joebritt/usb2cmi_lightpen/interface_photos/V2/IMG_20200309_125538.jpg

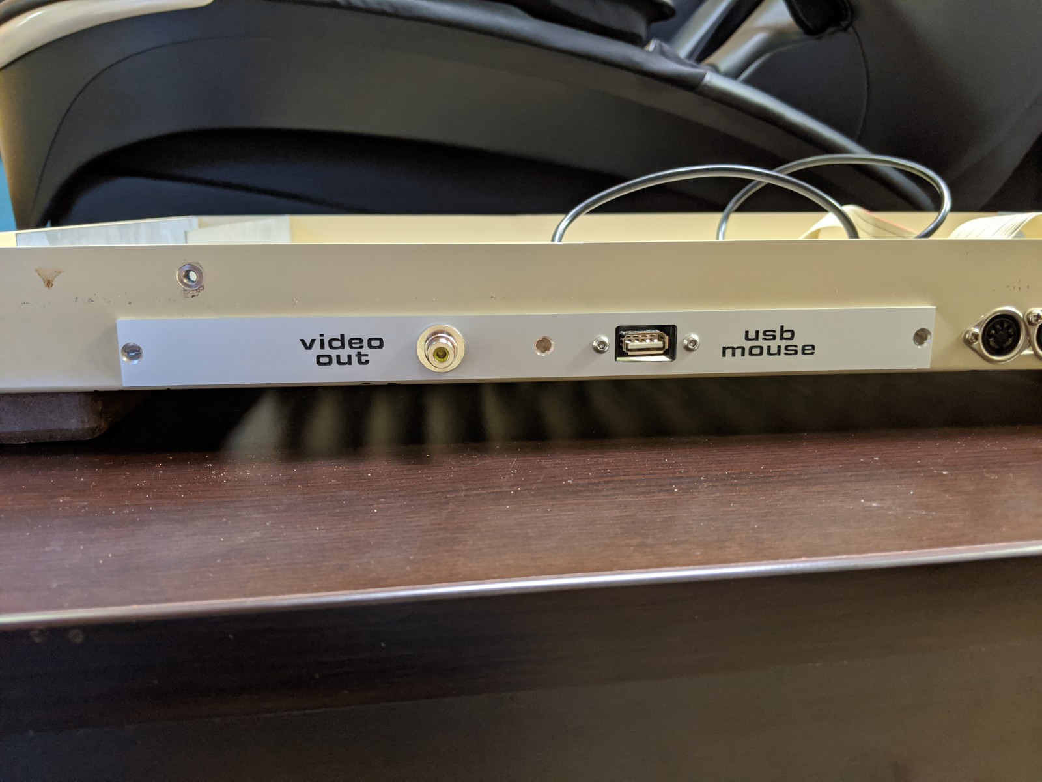
interface_photos/V2/IMG_20200309_125538.jpg
