joebritt/usb2cmi_lightpen/interface_photos/V2/IMG_20200321_205620.jpg

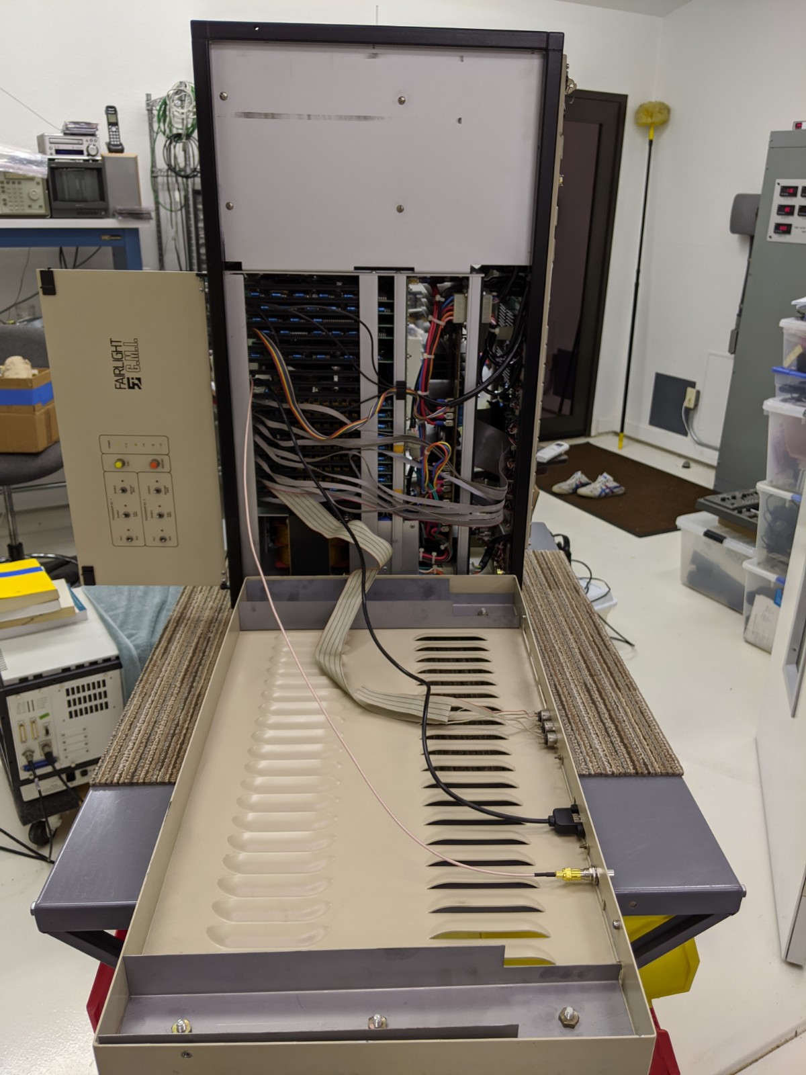
interface_photos/V2/IMG_20200321_205620.jpg
