joebritt/usb2cmi_lightpen/interface_photos/V2/IMG_20200321_212625.jpg

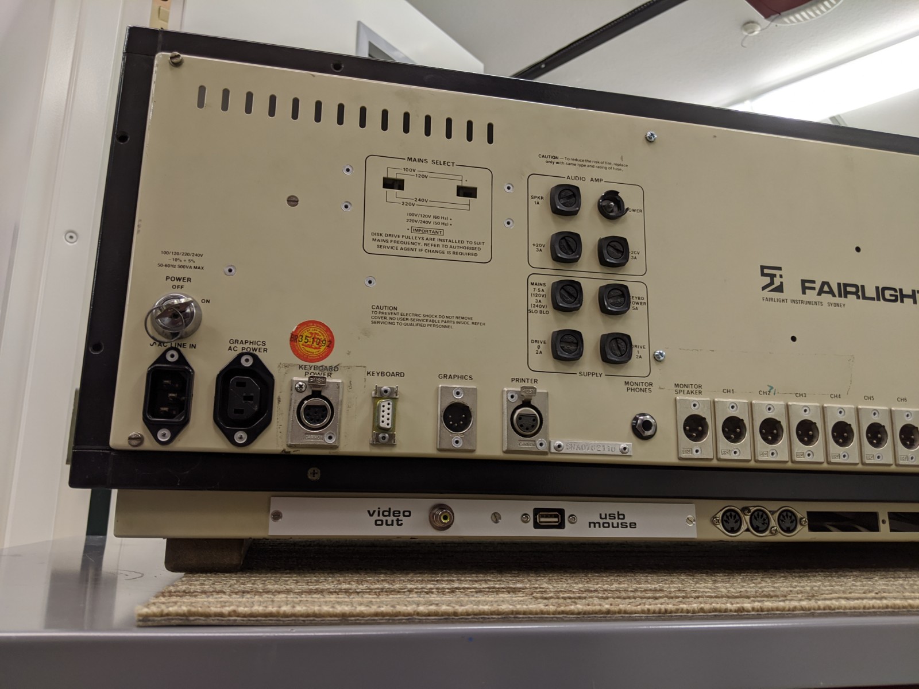
interface_photos/V2/IMG_20200321_212625.jpg
