joebritt/usb2cmi_lightpen/interface_photos/V2/IMG_20200322_163101.jpg

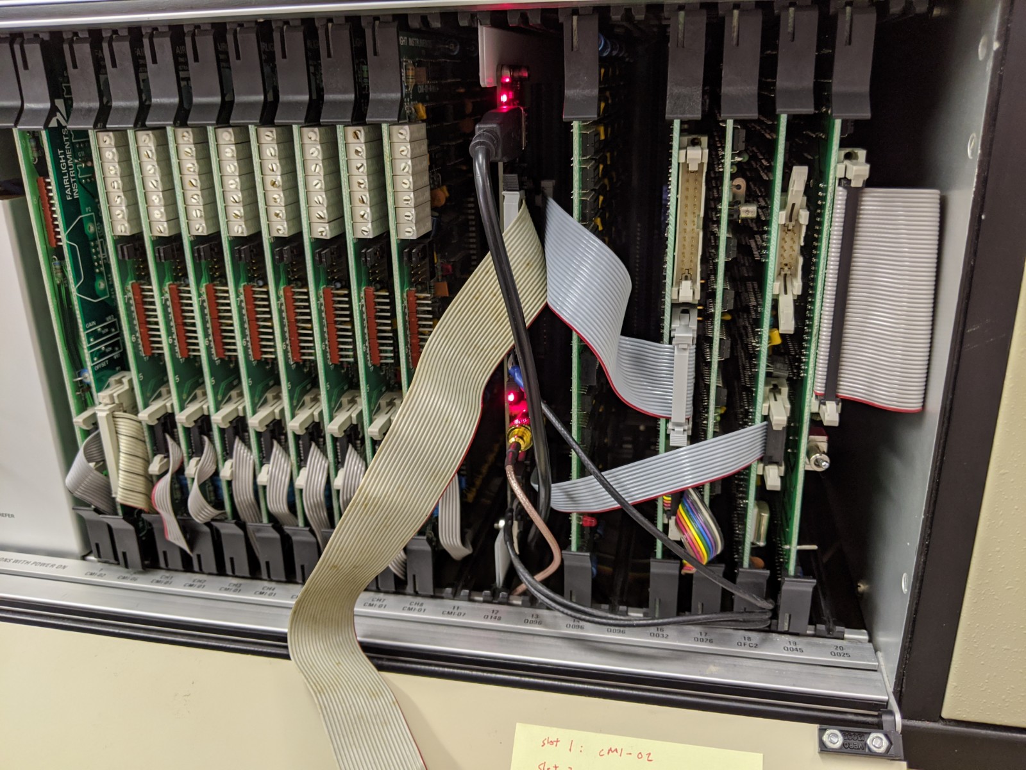
interface_photos/V2/IMG_20200322_163101.jpg
