joebritt/usb2cmi_lightpen/interface_photos/V2/IMG_20200322_164144.jpg

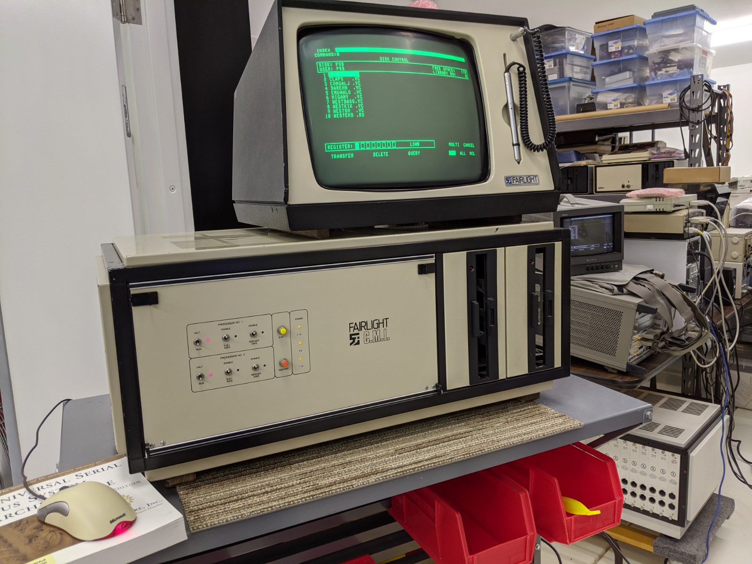
interface_photos/V2/IMG_20200322_164144.jpg
