joebritt/usb2cmi_lightpen/mouse/2x_only_pos.h

// This table was generated with an excel spreadsheet.
//
// The clock used to drive the Output Compare pulse generator runs at
// 80MHz.  The CMI dotclock is 10.38MHz.
//
// The screen is broken into 5 horizontal zones, and the number of
// 80MHz clocks we count to get into the pixel position we want
// varies depending on which zone the cursor is in.

int pixel_offsets[512] = { 
1017, 
1025, 
1033, 
1041, 
1048, 
1056, 
1064, 
1071, 
1079, 
1087, 
1095, 
1102, 
1110, 
1118, 
1125, 
1133, 
1141, 
1149, 
1156, 
1164, 
1172, 
1179, 
1187, 
1195, 
1202, 
1210, 
1218, 
1226, 
1233, 
1241, 
1249, 
1256, 
1264, 
1272, 
1280, 
1287, 
1295, 
1303, 
1310, 
1318, 
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
};
