joebritt/usb2cmi_lightpen/mouse/pos_II.h

// This table was generated with an excel spreadsheet.
//
// The clock used to drive the Output Compare pulse generator runs at
// 80MHz.  The Series I/II CMI dotclock is 10.65MHz.
//
// Note that the Q045 graphics card has 2 pots (RV1 and RV2) that 
// control one-shots which determine the active area location
// and width.
// Because of that, it is not safe for us to assume hard values
// for the bias offset and right edge of the screen.
// For Q045 systems, we allow the cursor to run off the screen on either side.
// We can safely pin the top and bottom positions, however.

unsigned int pixel_offsets_II[512] = { 
900,
908,
916,
923,
931,
938,
946,
953,
961,
968,
976,
983,
991,
998,
1006,
1013,
1021,
1028,
1036,
1043,
1051,
1058,
1066,
1073,
1081,
1088,
1096,
1103,
1111,
1118,
1126,
1133,
1141,
1148,
1156,
1163,
1171,
1178,
1186,
1193,
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
};
