joebritt/usb2cmi_lightpen/bootloader/boot_config.h

/*
*******************************************************************************
                                                                                
Software License Agreement                                                      
                                                                                
Copyright © 2007-2008 Microchip Technology Inc. and its licensors.  All         
rights reserved.                                                                
                                                                                
Microchip licenses to you the right to: (1) install Software on a single        
computer and use the Software with Microchip 16-bit microcontrollers and        
16-bit digital signal controllers ("Microchip Product"); and (2) at your        
own discretion and risk, use, modify, copy and distribute the device            
driver files of the Software that are provided to you in Source Code;           
provided that such Device Drivers are only used with Microchip Products         
and that no open source or free software is incorporated into the Device        
Drivers without Microchip's prior written consent in each instance.             
                                                                                
You should refer to the license agreement accompanying this Software for        
additional information regarding your rights and obligations.                   
                                                                                
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
*******************************************************************************

The boot loader uses three interfaces to define and customize its behavior.

Boot Loader IO Interface:

The boot loader IO interface definitions provide control inputs and status
outputs that the boot loader can use to determine when it should load a new
application image and how it should report its status.

Boot Loader Media Interface:

The boot loader media interface definitions provide access to the boot image 
medium and the ability to read the file.

Boot Loader Interface

The Loader interface definitions provide any data translation and Flash 
programming necessary to load the boot image into program Flash memory.

These interface routines can be implemented via macros or functions as 
required.
*******************************************************************************

 Change History:
  Rev   Description
  ----  -----------------------------------------
  2.7   Updated to include the PIC32 device information.

        Updated to include additional error codes (BL_FILE_NO_DATA, 
        LOADER_MISSING_START, LOADER_ALIGNMENT, LOADER_ERR, and
        LOADER_EOF_REC_MISSING)

*******************************************************************************
*/

/* Boot Status Codes
**************************************************************************
BOOT_STATUS is used to identify the current status of the boot loader.
**************************************************************************
*/

typedef enum
{
    // Boot loader status
    BL_RESET = 0,           // Device has been reset
    BL_LOADING,             // Loading of a new application image activated
    BL_TRANSPORT_INIT,      // Boot loader transport layer initialized
    BL_MEDIUM_DETACH,       // Indicates that the boot medium has been detached
    BL_FOUND_FILE,          // New application image file has been found
    BL_PROGRAMMED,          // The application image has been programmed to Flash
    BL_BOOTING,             // Booting application image

    // Transport-specific errors
    BL_USB_OC_ERR,          // USB Over-current error detected
    BL_FS_INIT_ERR,         // Unable to initialize the boot medium's file system
    BL_USB_HUB_ERR,         // USB hub error (hubs not supported)
    BL_BAD_DEV_ERR,         // Unsupported USB device attached
    USB_ENUM_ERR,           // Unable to enumerate USB device
    USB_MSD_INIT_ERR,       // Unable to initialize USB MSD client driver
    OUT_OF_MEMORY_ERR,      // Attempted to malloc memory and failed
    BL_FILE_ERR,            // Unable to open the boot image file
    BL_FILE_NO_DATA,        // Unable to read data from file but file did not report EOF
    USB_ERR,                // Unspecified USB error

    // Loader Errors
    LOADER_ADDRESS_LOW,     // Flash block address is out of range, low
    LOADER_ADDRESS_HIGH,    // Flash block address is out of range, high
    LOADER_CHECKSUM_ERR,    // Hex record checksum didn't match
    LOADER_FLASH_ERASE_ERR, // Erase had an error
    LOADER_FLASH_WRITE_ERR, // Unable to write to Flash
    LOADER_FLASH_VERIFY_ERR,// Data written to Flash did not match buffer data
    LOADER_MISSING_START,   // Start code was missing from the start of a line
    LOADER_ALIGNMENT,       // There was an issue with the data alignment
    LOADER_ERR,             // Unspecified error in the loader
    LOADER_EOF_REC_MISSING, // Reached the end of the file stream without a hex EOF record

    // General errors
    BL_BOOT_FAIL,           // Application not valid or failed to launch
    BL_FILE_NOT_FOUND       // Application image file not found

} BOOT_STATUS; 


/*
*******************************************************************************
Boot Loader IO Configuration
*******************************************************************************
*/

/* Boot Loader IO Call Out Interfaces
*******************************************************************************
The following interfaces are defined by macros and called from the boot loader 
to customize and define its control and status IO behavior.
*******************************************************************************
*/

#define BLIO_LoaderEnabled()    TRUE

extern volatile BOOT_STATUS BootStatus;
//#define BLIO_ReportBootStatus(s,z)            (BootStatus=(s))
//#define BLIO_ReportBootStatus(s,z)            Serial_BootStatus(s,z)
void BLIO_ReportBootStatus ( BOOT_STATUS status, char *message );

//*****************************************************************************
// Boot Loader Media Interface Configuration
//*****************************************************************************

// Application Image File Name
#define BOOT_FILE_NAME          "cmimouse.hex"

// Defines the size of the buffer used to read the boot image file.
#define BL_READ_BUFFER_SIZE     512


/* Boot Loader Media Interface Call Outs
*******************************************************************************
The following interface routines are called from the boot loader to access new
application image file and program it to Flash.
*******************************************************************************
*/

#define BLMedia_InitializeTransport()       USBInitialize(0)

#if defined(__PIC32__)
#define BLMedia_DeinitializeTransport()     (USBHostShutdown(),IFS1CLR = 0x02000000)
#else
#define BLMedia_DeinitializeTransport()     (USBHostShutdown())
#endif

#define BLMedia_MediumAttached()            USBHostMSDSCSIMediaDetect()


/* "Loader" Interface Call Outs
*******************************************************************************
The following interface is used by the media layer to decode and program the 
image file to memory.
*******************************************************************************
*/

// These macros define the maximum size of a Flash block.

#if defined(__32MX460F512L__) || \
    defined(__32MX440F512H__) || \
    defined(__32MX775F512L__) || \
    defined(__32MX675F512L__) || \
    defined(__32MX695F512L__) || \
    defined(__32MX795F512L__) || \
    defined(__32MX575F512L__) || \
    defined(__32MX795F512H__) || \
    defined(__32MX775F512H__) || \
    defined(__32MX695F512H__) || \
    defined(__32MX675F512H__) || \
    defined(__32MX575F512H__)

    #define FLASH_BLOCK_SIZE            (1024 * 4)          // Size in bytes

    //This set of options will only work with optimazation setting -Os
    //  Address of main application's Startup code
    #define APPLICATION_ADDRESS         0x9D00E000
    //  Base address and length of user flash block
    #define PROGRAM_FLASH_BASE          0x1D00E000          // Physical address
    #define PROGRAM_FLASH_LENGTH        0x00072000          // Length in bytes

//    //This set of options will only work with optimazation settings -Os, -O1, and -O2
//    //  Address of main application's Startup code
//    #define APPLICATION_ADDRESS         0x9D010000
//    //  Base address and length of user flash block
//    #define PROGRAM_FLASH_BASE          0x1D010000          // Physical address
//    #define PROGRAM_FLASH_LENGTH        0x00070000          // Length in bytes
//
//    //This set of options will work with all optimazation settings
//    //  Address of main application's Startup code
//    #define APPLICATION_ADDRESS         0x9D017000
//    //  Base address and length of user flash block
//    #define PROGRAM_FLASH_BASE          0x1D017000          // Physical address
//    #define PROGRAM_FLASH_LENGTH        0x00069000          // Length in bytes

#elif defined(__32MX460F256L__) || \
      defined(__32MX440F256H__) || \
      defined(__32MX775F256L__) || \
      defined(__32MX675F256L__) || \
      defined(__32MX575F256L__) || \
      defined(__32MX775F256H__) || \
      defined(__32MX675F256H__) || \
      defined(__32MX575F256H__)

    #define FLASH_BLOCK_SIZE            (1024 * 4)          // Size in bytes

    //This set of options will only work with optimazation setting -Os
    //  Address of main application's Startup code
    #define APPLICATION_ADDRESS         0x9D00E000
    //  Base address and length of user flash block
    #define PROGRAM_FLASH_BASE          0x1D00E000          // Physical address
    #define PROGRAM_FLASH_LENGTH        0x00032000          // Length in bytes

//    //This set of options will work with all optimazation settings
//    //  Address of main application's Startup code
//    #define APPLICATION_ADDRESS         0x9D017000
//    //  Base address and length of user flash block
//    #define PROGRAM_FLASH_BASE          0x1D017000          // Physical address
//    #define PROGRAM_FLASH_LENGTH        0x00029000          // Length in bytes
//
//    //This set of options will only work with optimazation settings -Os, -O1, and -O2
//    //  Address of main application's Startup code
//    #define APPLICATION_ADDRESS         0x9D010000
//    //  Base address and length of user flash block
//    #define PROGRAM_FLASH_BASE          0x1D010000          // Physical address
//    #define PROGRAM_FLASH_LENGTH        0x00030000          // Length in bytes

#elif defined(__32MX440F128H__) || \
      defined(__32MX440F128L__)

    #define FLASH_BLOCK_SIZE            (1024 * 4)          // Size in bytes

// Joe Britt -- this seems to work with optimizations setting -01
    //  Address of main application's Startup code
    #define APPLICATION_ADDRESS         0x9D00D000
    //  Base address and length of user flash block
    #define PROGRAM_FLASH_BASE          0x1D00D000          // Physical address
    #define PROGRAM_FLASH_LENGTH        0x00013000          // Length in bytes

// Joe Britt -- this was the setting I was using, then I realized it looks like I can squeeze
//              things for some more space
//    //This set of options will only work with optimazation setting -Os
//    //  Address of main application's Startup code
//    #define APPLICATION_ADDRESS         0x9D00E000
//    //  Base address and length of user flash block
//    #define PROGRAM_FLASH_BASE          0x1D00E000          // Physical address
//    #define PROGRAM_FLASH_LENGTH        0x00012000          // Length in bytes

//    //This set of options will only work with optimazation settings -Os, -O1, and -O2
//    //  Address of main application's Startup code
//    #define APPLICATION_ADDRESS         0x9D010000
//    //  Base address and length of user flash block
//    #define PROGRAM_FLASH_BASE          0x1D010000          // Physical address
//    #define PROGRAM_FLASH_LENGTH        0x00010000          // Length in bytes
//    
//    //This set of options will work with all optimazation settings
//    //  Address of main application's Startup code
//    #define APPLICATION_ADDRESS         0x9D017000
//    //  Base address and length of user flash block
//    #define PROGRAM_FLASH_BASE          0x1D017000          // Physical address
//    #define PROGRAM_FLASH_LENGTH        0x00009000          // Length in bytes


#elif defined(__PIC24F__)

#define APPLICATION_ADDRESS         0xA000

// These macros define the maximum size of a Flash block.
#define PROGRAM_FLASH_BASE          0x0000A000          // Physical address
//#define PROGRAM_FLASH_LENGTH        0x00020C00          // Length in bytes - this includes the configuration words
#define PROGRAM_FLASH_LENGTH        0x00020800          // Length in bytes - this does not include the configuration words

#define FLASH_BLOCK_SIZE            (1024)          // Size in bytes

#else
    #error "Device currently supported"
#endif

// Optional Record Type Support (Necessary if EXTENDED_HEXFILE_SUPPORT is defined)
#define Loader_ValidateSerialNumber(d,l)    RECORD_NON_DATA
#define Loader_ValidateRevisionNumber(d,l)  RECORD_NON_DATA
#define Loader_CheckErrorDetection(d,l)     RECORD_NON_DATA

#define Loader_PermitProgramming()          TRUE


/*
*******************************************************************************
EOF
*******************************************************************************
*/
