joebritt/usb2cmi_lightpen/bootloader/boot_io.c

/*
********************************************************************************
                                                                                
Software License Agreement                                                      
                                                                                
Copyright © 2008 Microchip Technology Inc. and its licensors.  All         
rights reserved.                                                                
                                                                                
Microchip licenses to you the right to: (1) install Software on a single        
computer and use the Software with Microchip 16-bit microcontrollers and        
16-bit digital signal controllers ("Microchip Product"); and (2) at your        
own discretion and risk, use, modify, copy and distribute the device            
driver files of the Software that are provided to you in Source Code;           
provided that such Device Drivers are only used with Microchip Products         
and that no open source or free software is incorporated into the Device        
Drivers without Microchip's prior written consent in each instance.             
                                                                                
You should refer to the license agreement accompanying this Software for        
additional information regarding your rights and obligations.                   
                                                                                
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
********************************************************************************
*/

#include "Compiler.h"
#include "GenericTypedefs.h"
#include "HardwareProfile.h"
#include "boot.h"

/*
*******************************************************************************
Boot Loader IO Configuration
*******************************************************************************
*/

// Calculates the CORE_TICK_PERIOD for the status LED blink period.
#ifndef FOSC
    #define FOSC                    72E6
#endif

#ifndef TOGGLES_PER_SEC
    #define TOGGLES_PER_SEC			10
#endif

#ifndef CORE_TICK_PERIOD
    #define CORE_TICK_PERIOD	    (FOSC/2/TOGGLES_PER_SEC)
#endif

// Selects the status LED (port B only) used to indicate boot status.
#ifndef BOOT_LED
    #define BOOT_LED                BIT_7
#endif


// Global Data
volatile unsigned int   TickPeriod;     // LED Flash timer tick

volatile BOOT_STATUS    BootStatus;     // Most recent boot status reported

BOOL                    SwitchPrimed;   // Boot switched released so it can
                                        // be used as an abort if needed


/****************************************************************************
  Function:
    void BLIO_InitializeIO ( void )

  Description:
    This routine initializes the status LED and boot switch ports.  It also 
    initializes the core timer so it can be used to flash the status LED.

  Precondition:
    None

  Parameters:
    None

  Returns:
    None

  Remarks:
    None
***************************************************************************/

void BLIO_InitializeIO ( void )
{
	hw_init();		// set up our board-specific i/o
}


/****************************************************************************
  Function:
    void BLIO_DeinitializeIO ( void )

  Description:
    This routine de-initializes the IO pins and disables and clears the core
    timer interrupt.

  Precondition:
    None

  Parameters:
    None

  Returns:
    None

  Remarks:
    Any stray pending interrupts (once the application boots) may cause
    the system to trigger an un-handled (or incorrectly handled) interrupt.
***************************************************************************/

void BLIO_DeinitializeIO ( void )
{
    //mDeInitAllLEDs();
}


/****************************************************************************
  Function:
    BOOL BLIO_AbortLoad ( void )

  Description:
    This routine is called to determine if the user needs to abort the load 
    of the new application after BLIO_LoaderEnabled has returned TRUE and the
    search for a new application image has began.  It is used to provides a 
    way out of the main loader loop if no image is available.

  Precondition:
    BLIO_InitializeIO must have been called.

  Parameters:
    None

  Returns:
    TRUE    - If the load attempt should be aborted
    FALSE   - If the load attempt should continue

  Remarks:
    Will not interrupt a load once it's actually started.
***************************************************************************/

BOOL BLIO_AbortLoad ( void )
{
    return FALSE;
}

/****************************************************************************
  Function:
    BOOL BLIO_LoaderEnabled ( void )

  Description:
    This routine is called to determine if the boot loader should attempt to
    load a new application.

  Precondition:
    BLIO_InitializeIO must have been called.

  Parameters:
    None

  Returns:
      TRUE  - If a new application should be loaded
      FALSE - If the existing application should be booted


  Remarks:
    This function must be implemented.
***************************************************************************/


/****************************************************************************
  Function:
    void BLIO_ReportBootStatus ( BOOT_STATUS status, char *message )

  Description:
    This function can be used to display the current status of the boot 
    loader and possibly a with a descriptive message.

  Precondition:
    BLIO_InitializeIO must have been called.

  Parameters:
    status      - A code indicating the current boot loader status
    message     - A text string describing the current status

  Returns:
    None

  Remarks:
    This function can be implemented in any way that is appropriate for the 
    device.  Not all of the information needs to be used.  A macro
    definition can be used to "throw away" the string to reduce the Flash 
    footprint of the boot loader.
***************************************************************************/


/*
*******************************************************************************
EOF
*******************************************************************************
*/
